rah2003/PyPortal-Pynt-RTK/docs/hardware/enclosure-d-band-inside.png

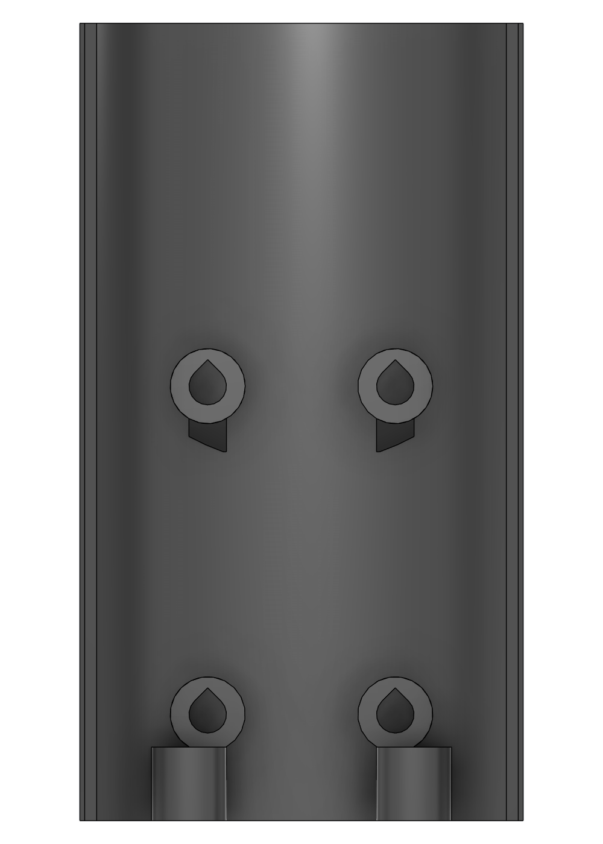
docs/hardware/enclosure-d-band-inside.png
