rah2003/PyPortal-Pynt-RTK/docs/hardware/enclosure-d-boss-closeup.png

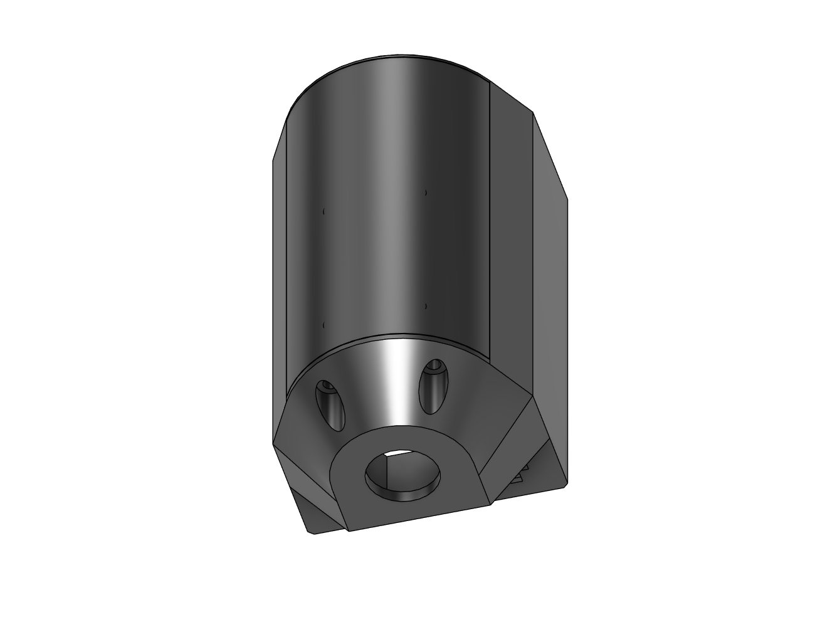
docs/hardware/enclosure-d-boss-closeup.png
