rah2003/PyPortal-Pynt-RTK/docs/hardware/enclosure-d-bottomleft.png

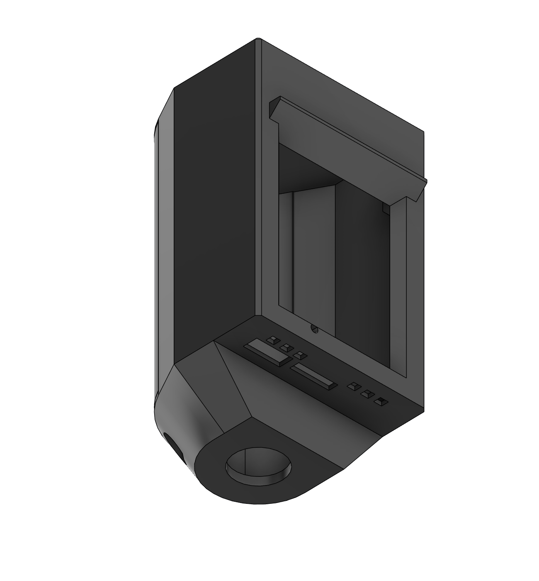
docs/hardware/enclosure-d-bottomleft.png
