rah2003/PyPortal-Pynt-RTK/docs/hardware/enclosure-d-front.png

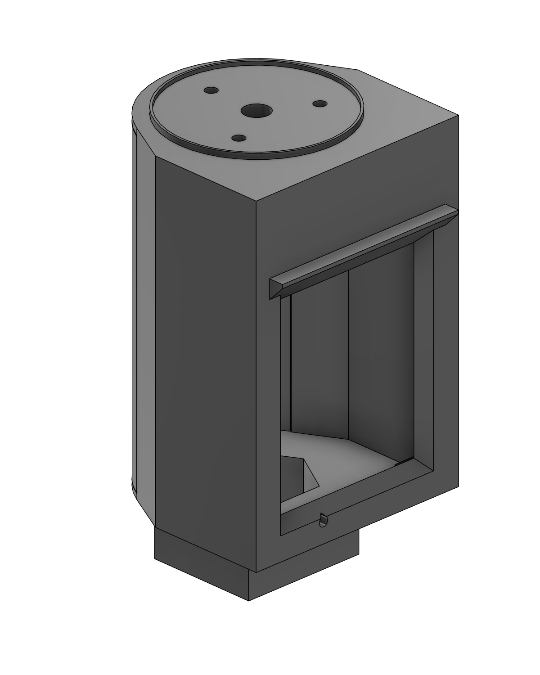
docs/hardware/enclosure-d-front.png
