rah2003/PyPortal-Pynt-RTK/docs/hardware/enclosure-d-plan-section.png

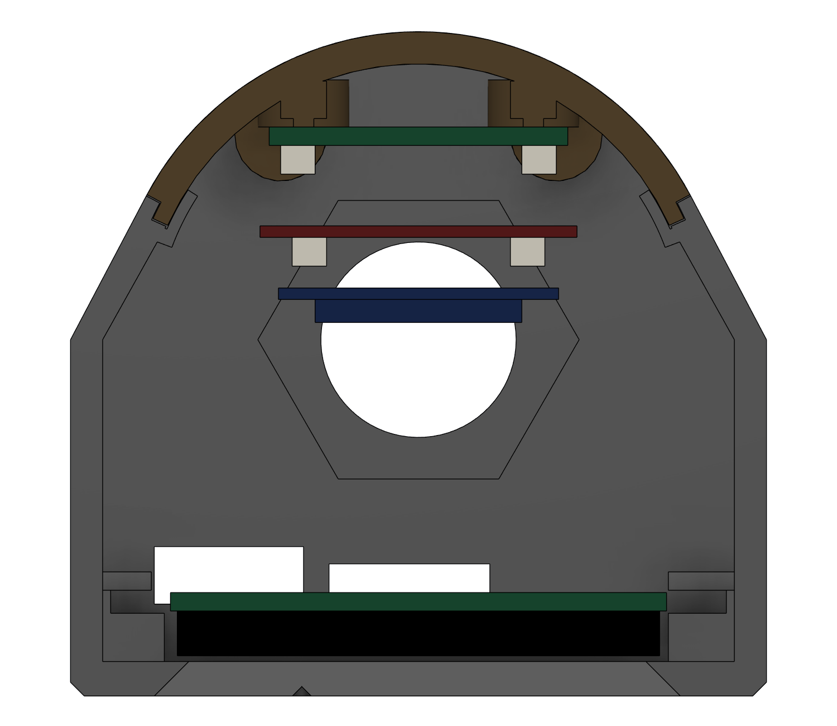
docs/hardware/enclosure-d-plan-section.png
