rah2003/PyPortal-Pynt-RTK/docs/hardware/enclosure-d-side.png

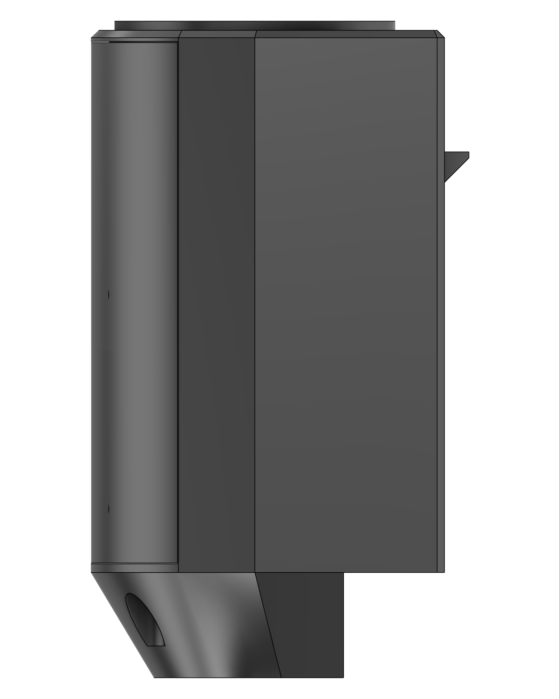
docs/hardware/enclosure-d-side.png
