rah2003/PyPortal-Pynt-RTK/docs/hardware/enclosure-d-strip-chamfers.png

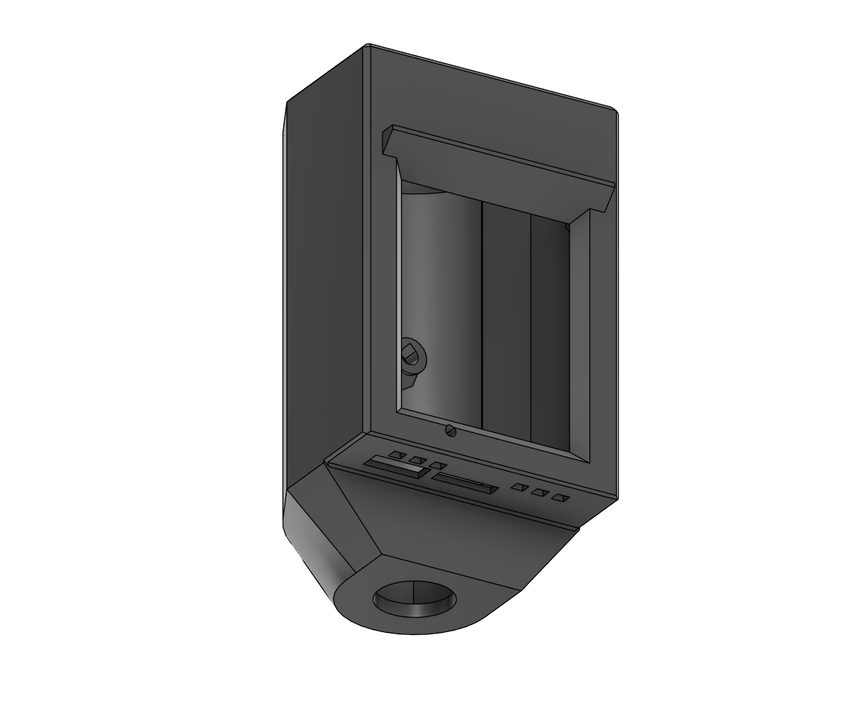
docs/hardware/enclosure-d-strip-chamfers.png
