rah2003/PyPortal-Pynt-RTK/docs/hardware/enclosure-d-top.png

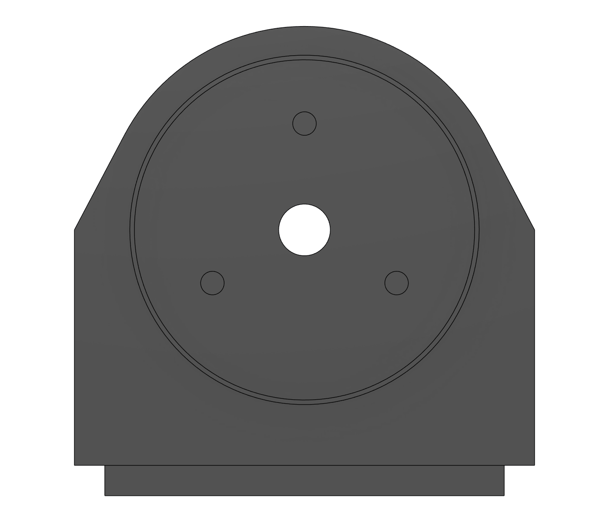
docs/hardware/enclosure-d-top.png
