rah2003/PyPortal-Pynt-RTK/docs/hardware/enclosure-assembly-iso.png

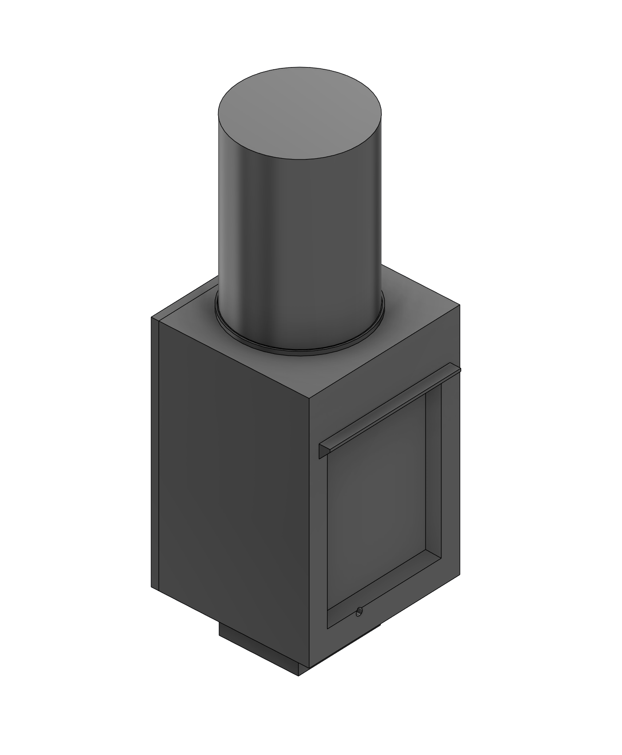
docs/hardware/enclosure-assembly-iso.png
