rah2003/PyPortal-Pynt-RTK/docs/hardware/enclosure-assembly-section.png

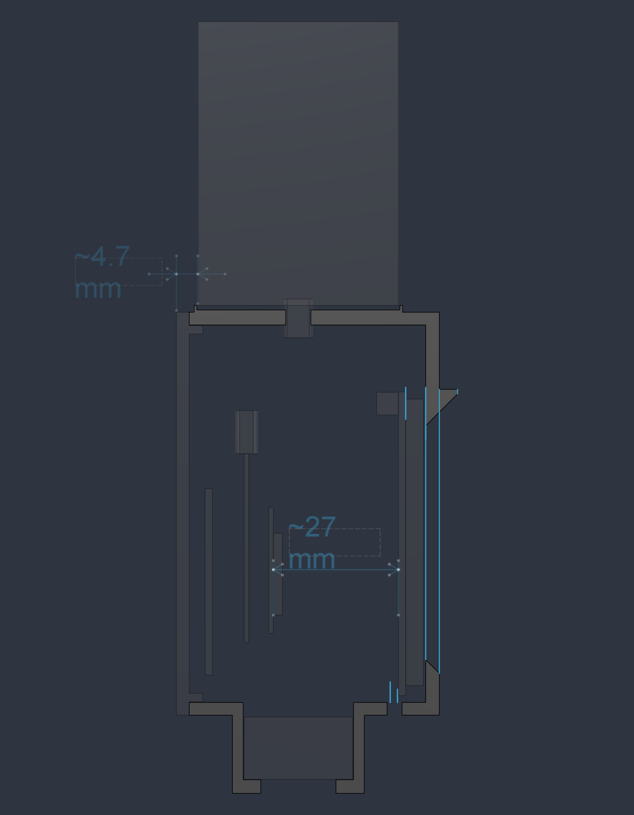
docs/hardware/enclosure-assembly-section.png
