rah2003/PyPortal-Pynt-RTK/docs/hardware/enclosure-assembly-top.png

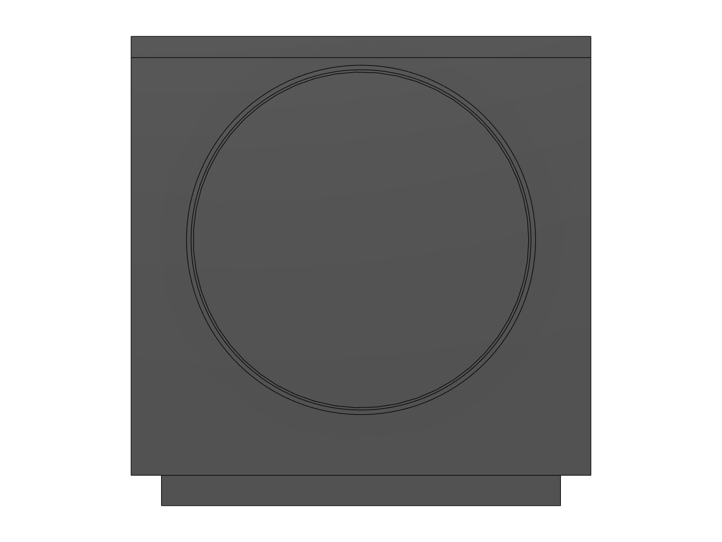
docs/hardware/enclosure-assembly-top.png
