rah2003/PyPortal-Pynt-RTK/docs/hardware/enclosure-d-assembly-section.png

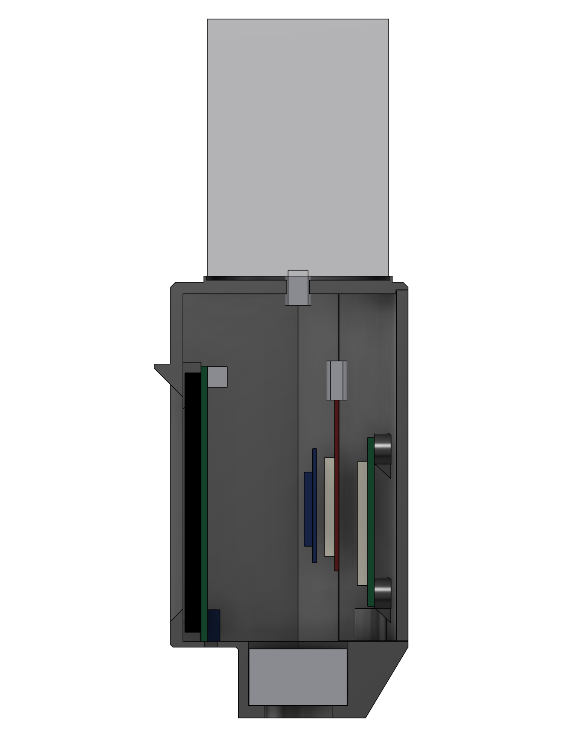
docs/hardware/enclosure-d-assembly-section.png
